jonsag/atTris/atTinyArcade-pio/src/Tetris_Attiny_Arcade.h

/* 2015 / 2016 /2017
   Tetris for Attiny Arcade
   ========================

   When the game is running :
   ==========================
   Tap LEFT BUTTON - Moves the piece to the left (and wraps around at the left edge)
   Hold LEFT BUTTON - Move the piece to the right
   Tap RIGHT BUTTON - Rotates the piece
   Hold RIGHT BUTTON - Place the piece

   Before the game starts:
   =======================
   Hold LEFT BUTTON - Turns 'ghost' piece on and off
   Hold RIGHT and LEFT BUTTONS together - Turns 'challenge mode' on and off (which fills the screens with random stuff at the start of the game to make
   it more tricky!)

   _________________________________________________________________________________________________________________________________________________________
   This version developed by Andy Jackson - Twitter @andyhighnumber - Tweet me if you have any problems getting this to compile or run.
   The code that does not fall under the licenses of sources listed below can be used non-commercially with or without attribution.
   This software is supplied without warranty of any kind.

   Designed for the Attiny85 and optimized for the #AttinyArcade platform. The source code is less than 8KB and the sketch
   should run happily with less than 300 bytes of RAM. You can find out more about this platform from http://webboggles.com/, buy kits
   to make it (or get instructions / schematics). This sketch includes some code from the #AttinyArcade games on that site, including interrupt code.

   This game started life as a port but is now essentially a clone of TinyTetris by Anthony Russell, with some additional features. There remain
   elements of that original codebase, although the vast majority of what's here has been rewritten from scratch (including the screen, text and number
   rendering code and much of the game engine) in order to optimize for memory, improve responsiveness and allow new features on the limited hardware
   (added features include High score (saved to EEPROM), optional Ghost (or Shadow) Piece, Interrupt Handling and Hard-Mode functionality).

   Anthony's source can be found here: https://github.com/AJRussell/Tiny-Tetris and is highly recommended if you'd like a version
   of Tetris to run on normal Arduino hardware. It has some lovely graphics by Tobozo (which sadly there's not space for on the Attiny85) and it's also
   possible that some code by Tobozo has made it into this version. Tobozo's repository can be found here; https://github.com/tobozo and is well worth a look.
   There is an Instructables page relating to this project here: https://www.instructables.com/id/Tetris-Clone-With-OLED-SSD1306I2C-for-Arduino-Nano/

   This sketch is using the screen control and font functions written by Neven Boyanov for the http://tinusaur.wordpress.com/ project
   Source code and font files available at: https://bitbucket.org/tinusaur/ssd1306xled - hacked about by Andy Jackson to make them
   render side-on for this game. All the necessary functions are in this file, there's no need to download any additional libraries to compile this game.

   The sleep code in this file is based on this blog post by Matthew Little:
   http://www.re-innovation.co.uk/web12/index.php/en/blog-75/306-sleep-modes-on-attiny85
*/

// The custom font file is the only additional file you should need to compile this game
#include "font8x8AJ.h"

// Standard Arduino headers
#include <EEPROM.h>
#include <avr/pgmspace.h>
#include <avr/sleep.h>
#include <avr/interrupt.h> // needed for the additional interrupt

// Mode settings for functions with multiple purposes
#define NORMAL 0
#define GHOST 1
#define FULL 0
#define PARTIAL 1
#define DRAW 0
#define ERASE 1

// The horizontal width of the playing area
#define HORIZ 10
// The vertical visible space of the playing area
#define VERTDRAW 19
// The size of the array of blocks (some are outside visible area to allow them to drop in from off screen)
#define VERTMAX 24

// The horizontal position where pieces begin
#define STARTX 3
// The vertical position where pieces begin
#define STARTY 19
// What level does the game start on
#define STARTLEVEL 1
// The multiplying factor that sets how the speed scales with level (one level increment for every row cleared)
#define LEVELFACTOR 4
// The number of milliseconds before each drop (baseline)
#define DROPDELAY 600

#define DIGITAL_WRITE_HIGH(PORT) PORTB |= (1 << PORT)
#define DIGITAL_WRITE_LOW(PORT) PORTB &= ~(1 << PORT)

// Routines to set and clear bits (used in the sleep code)
#define cbi(sfr, bit) (_SFR_BYTE(sfr) &= ~_BV(bit))
#define sbi(sfr, bit) (_SFR_BYTE(sfr) |= _BV(bit))

// Defines for OLED output
#define SSD1306XLED_H
#define SSD1306_SCL PORTB4 // SCL, Pin 4 on SSD1306 Board - for webbogles board
#define SSD1306_SDA PORTB3 // SDA, Pin 3 on SSD1306 Board - for webbogles board
#define SSD1306_SA 0x78    // Slave address

// The bitmaps for the little images of next block
static const byte miniBlock[][4] PROGMEM = {
    {0x77, 0x77, 0x00, 0x00},
    {0x70, 0x77, 0x70, 0x00},
    {0x70, 0x00, 0x70, 0x77},
    {0x70, 0x07, 0x70, 0x07},
    {0x70, 0x07, 0x00, 0xEE},
    {0x70, 0x77, 0x00, 0x0E},
    {0x70, 0x07, 0xEE, 0x00}};

// The bitmaps for the main blocks
static const int blocks[7] PROGMEM = {
    0x4444, 0x44C0,
    0x4460, 0x0660,
    0x06C0, 0x0E40,
    0x0C60};

// The bitmaps for blocks on the screen
static const byte blockout[16] PROGMEM = {
    0xF8, 0x00, 0x3E, 0x80,
    0x0F, 0xE0, 0x03, 0xF8,
    0x3E, 0x80, 0x0F, 0xE0,
    0x03, 0xF8, 0x3E, 0x00};

// The bitmaps for ghost blocks on the screen
static const byte ghostout[16] PROGMEM = {
    0x88, 0x00, 0x22, 0x80,
    0x08, 0x20, 0x02, 0x88,
    0x22, 0x80, 0x08, 0x20,
    0x02, 0x88, 0x22, 0x00};

// Decode lookup to translate block positions to the 8 columns on the screen
static const byte startDecode[11] PROGMEM = {0, 1, 1, 2, 3, 4, 4, 5, 6, 7, 8};
static const byte endDecode[11] PROGMEM = {1, 2, 3, 3, 4, 5, 6, 6, 7, 8, 8};

// Function prototypes - generic ones I use in all games
void doNumber(int x, int y, int value);
void beep(int, int);

// Function prototypes - screen control modified from https://bitbucket.org/tinusaur/ssd1306xled
void ssd1306_init(void);
void ssd1306_xfer_start(void);
void ssd1306_xfer_stop(void);
void ssd1306_send_byte(uint8_t byte);
void ssd1306_send_command(uint8_t command);
void ssd1306_send_data_start(void);
void ssd1306_send_data_stop(void);
void ssd1306_setpos(uint8_t x, uint8_t y);
void ssd1306_fillscreen(uint8_t fill_Data);
void ssd1306_char_f8x8(uint8_t x, uint8_t y, const char ch[]);

// Function prototypes - tetris-specific
void playTetris(void);
void handleInput(void);

void drawScreen(int startCol, int endCol, int startRow, int endRow, byte mode);
void drawScreenBorder(void);

byte readBlockArray(byte x, byte y);
void writeblockArray(byte x, byte y, bool value);
byte readGhostArray(byte x, byte y);
void writeGhostArray(byte x, byte y, bool value);
void fillGrid(byte value, bool mode);

void rotatePiece(void);
bool movePieceDown(void);
void movePieceLeft(void);
void movePieceRight(void);
byte checkCollision(void);

bool createGhost(void);
void drawGhost(byte action);
void loadPiece(byte pieceNumber, byte row, byte column);
void drawPiece(byte action);
void setNextBlock(byte pieceNumber);

// Variables
struct pieceSpace
{
  byte blocks[4][4];
  int row;
  int column;
};

pieceSpace currentPiece = {0}; // The piece in play
pieceSpace oldPiece = {0};     // Buffer to hold the current piece whilst its manipulated
pieceSpace ghostPiece = {0};   // Current ghost piece

unsigned long moveTime = 0; // Baseline time for current move
unsigned long keyTime = 0;  // Baseline time for current keypress

byte keylock = 0; // Holds the mode of the last keypress (for debounce and stuff)

byte nextBlockBuffer[8][2]; // The little image of the next block
byte nextPiece = 0;         // The identity of the next piece
byte blockArray[HORIZ][3];  // The byte-array of blocks
byte ghostArray[HORIZ][3];  // The byte-array of ghost pieces
bool stopAnimate;           // True when the game is running

int lastGhostRow = 0; // Buffer to hold previous ghost position - for accurate drawing
int score = 0;        // Score buffer
int topScore = 0;     // High score buffer

bool challengeMode = 0; // Is the system in "Hard" mode?
bool ghost = 1;         // Is the ghost active?

int level = 0; // Current level (increments once per cleared line)

void doNumber(int x, int y, int value)
{
  char temp[10] = {0, 0, 0, 0, 0, 0, 0, 0, 0, 0};
  itoa(value, temp, 10);
  ssd1306_char_f8x8(x, y, temp);
}

void beep(int bCount, int bDelay)
{
  for (int i = 0; i <= bCount; i++)
  {
    digitalWrite(1, HIGH);
    for (int i2 = 0; i2 < bDelay; i2++)
    {
      __asm__("nop\n\t");
    }
    digitalWrite(1, LOW);
    for (int i2 = 0; i2 < bDelay; i2++)
    {
      __asm__("nop\n\t");
    }
  }
}

void ssd1306_char_f8x8(uint8_t x, uint8_t y, const char ch[])
{
  uint8_t c, i, j = 0;

  while (ch[j] != '\0')
  {
    c = ch[j] - 32; // to space
    if (c > 0)
      c = c - 12; // to dash
    if (c > 15)
      c = c - 7;
    if (c > 40)
      c = c - 6;

    ssd1306_setpos(y, x);
    ssd1306_send_data_start();
    for (byte lxn = 0; lxn < 8; lxn++)
    {
      ssd1306_send_byte(pgm_read_byte(&font[c][7 - lxn]));
    }
    ssd1306_send_data_stop();
    x += 1;
    j++;
  }
}

// Interrupt handlers - to make sure every button press is caught promptly!
ISR(PCINT0_vect)
{ // PB0 pin button interrupt
  if (keylock == 0)
  {
    keylock = 1;
    keyTime = millis();
  }
}
void playerIncTetris()
{ // PB2 pin button interrupt
  if (keylock == 0)
  {
    keylock = 2;
    keyTime = millis();
  }
}

// Screen control functions
void ssd1306_init(void)
{
  DDRB |= (1 << SSD1306_SDA); // Set port as output
  DDRB |= (1 << SSD1306_SCL); // Set port as output

  ssd1306_send_command(0xAE); // display off
  ssd1306_send_command(0x00); // Set Memory Addressing Mode
  ssd1306_send_command(0x10); // 00,Horizontal Addressing Mode;01,VERTDRAWical Addressing Mode;10,Page Addressing Mode (RESET);11,Invalid
  ssd1306_send_command(0x40); // Set Page Start Address for Page Addressing Mode,0-7
  ssd1306_send_command(0x81); // Set COM Output Scan Direction
  ssd1306_send_command(0xCF); // ---set low column address
  ssd1306_send_command(0xA1); // ---set high column address
  ssd1306_send_command(0xC8); // --set start line address
  ssd1306_send_command(0xA6); // --set contrast control register
  ssd1306_send_command(0xA8);
  ssd1306_send_command(0x3F); // --set segment re-map 0 to 127
  ssd1306_send_command(0xD3); // --set normal display
  ssd1306_send_command(0x00); // --set multiplex ratio(1 to 64)
  ssd1306_send_command(0xD5); //
  ssd1306_send_command(0x80); // 0xa4,Output follows RAM content;0xa5,Output ignores RAM content
  ssd1306_send_command(0xD9); // -set display offset
  ssd1306_send_command(0xF1); // -not offset
  ssd1306_send_command(0xDA); // --set display clock divide ratio/oscillator frequency
  ssd1306_send_command(0x12); // --set divide ratio
  ssd1306_send_command(0xDB); // --set pre-charge period
  ssd1306_send_command(0x40); //
  ssd1306_send_command(0x20); // --set com pins hardware configuration
  ssd1306_send_command(0x02);
  ssd1306_send_command(0x8D); // --set vcomh
  ssd1306_send_command(0x14); // 0x20,0.77xVcc
  ssd1306_send_command(0xA4); // --set DC-DC enable
  ssd1306_send_command(0xA6); //
  ssd1306_send_command(0xAF); // --turn on oled panel
}

void ssd1306_xfer_start(void)
{
  DIGITAL_WRITE_HIGH(SSD1306_SCL); // Set to HIGH
  DIGITAL_WRITE_HIGH(SSD1306_SDA); // Set to HIGH
  DIGITAL_WRITE_LOW(SSD1306_SDA);  // Set to LOW
  DIGITAL_WRITE_LOW(SSD1306_SCL);  // Set to LOW
}

void ssd1306_xfer_stop(void)
{
  DIGITAL_WRITE_LOW(SSD1306_SCL);  // Set to LOW
  DIGITAL_WRITE_LOW(SSD1306_SDA);  // Set to LOW
  DIGITAL_WRITE_HIGH(SSD1306_SCL); // Set to HIGH
  DIGITAL_WRITE_HIGH(SSD1306_SDA); // Set to HIGH
}

void ssd1306_send_byte(uint8_t byte)
{
  uint8_t i;
  for (i = 0; i < 8; i++)
  {
    if ((byte << i) & 0x80)
      DIGITAL_WRITE_HIGH(SSD1306_SDA);
    else
      DIGITAL_WRITE_LOW(SSD1306_SDA);

    DIGITAL_WRITE_HIGH(SSD1306_SCL);
    DIGITAL_WRITE_LOW(SSD1306_SCL);
  }
  DIGITAL_WRITE_HIGH(SSD1306_SDA);
  DIGITAL_WRITE_HIGH(SSD1306_SCL);
  DIGITAL_WRITE_LOW(SSD1306_SCL);
}

void ssd1306_send_command(uint8_t command)
{
  ssd1306_xfer_start();
  ssd1306_send_byte(SSD1306_SA); // Slave address, SA0=0
  ssd1306_send_byte(0x00);       // write command
  ssd1306_send_byte(command);
  ssd1306_xfer_stop();
}

void ssd1306_send_data_start(void)
{
  ssd1306_xfer_start();
  ssd1306_send_byte(SSD1306_SA);
  ssd1306_send_byte(0x40); // write data
}

void ssd1306_send_data_stop(void)
{
  ssd1306_xfer_stop();
}

void ssd1306_setpos(uint8_t x, uint8_t y)
{
  if (y > 7)
    return;
  ssd1306_xfer_start();
  ssd1306_send_byte(SSD1306_SA); // Slave address,SA0=0
  ssd1306_send_byte(0x00);       // write command

  ssd1306_send_byte(0xb0 + y);
  ssd1306_send_byte(((x & 0xf0) >> 4) | 0x10); // |0x10
  ssd1306_send_byte((x & 0x0f) | 0x01);        // |0x01

  ssd1306_xfer_stop();
}

void ssd1306_fillscreen(uint8_t fill_Data)
{
  uint8_t m, n;
  for (m = 0; m < 8; m++)
  {
    ssd1306_send_command(0xb0 + m); // page0-page1
    ssd1306_send_command(0x00);     // low column start address
    ssd1306_send_command(0x10);     // high column start address
    ssd1306_send_data_start();
    for (n = 0; n < 128; n++)
    {
      ssd1306_send_byte(fill_Data);
    }
    ssd1306_send_data_stop();
  }
}

// Sleep code from http://www.re-innovation.co.uk/web12/index.php/en/blog-75/306-sleep-modes-on-attiny85
void system_sleep()
{
  ssd1306_fillscreen(0x00);
  ssd1306_send_command(0xAE);
  cbi(ADCSRA, ADEN);                   // switch Analog to DigitalconVERTDRAWer OFF
  set_sleep_mode(SLEEP_MODE_PWR_DOWN); // sleep mode is set here
  sleep_enable();
  sleep_mode();      // System actually sleeps here
  sleep_disable();   // System continues execution here when watchdog timed out
  sbi(ADCSRA, ADEN); // switch Analog to DigitalconVERTDRAWer ON
  ssd1306_send_command(0xAF);
}

byte readBlockArray(byte x, byte y)
{
  if (y < 8)
  {
    return ((blockArray[x][0] & B00000001 << y) >> y);
  }
  else if (y > 15)
  {
    return ((blockArray[x][2] & B00000001 << y - 15) >> y - 15);
  }
  else
  {
    return ((blockArray[x][1] & B00000001 << y - 8) >> y - 8);
  }
}

void writeblockArray(byte x, byte y, bool value)
{
  byte arr = 0;
  if (y < 8)
  {
    // do nothing
  }
  else if (y > 15)
  {
    arr = 2;
    y -= 15;
  }
  else
  {
    arr = 1;
    y -= 8;
  }
  if (value == 1)
    blockArray[x][arr] |= B00000001 << y;
  else
    blockArray[x][arr] &= (B11111110 << y) | (B01111111 >> 7 - y);
}

byte readGhostArray(byte x, byte y)
{
  if (y < 8)
  {
    return ((ghostArray[x][0] & B00000001 << y) >> y);
  }
  else if (y > 15)
  {
    return ((ghostArray[x][2] & B00000001 << y - 15) >> y - 15);
  }
  else
  {
    return ((ghostArray[x][1] & B00000001 << y - 8) >> y - 8);
  }
}

void writeGhostArray(byte x, byte y, bool value)
{
  byte arr = 0;
  if (y < 8)
  {
    // do nothing
  }
  else if (y > 15)
  {
    arr = 2;
    y -= 15;
  }
  else
  {
    arr = 1;
    y -= 8;
  }
  if (value == 1)
    ghostArray[x][arr] |= B00000001 << y;
  else
    ghostArray[x][arr] &= (B11111110 << y) | (B01111111 >> 7 - y);
}

void fillGrid(byte value, bool mode)
{
  for (char r = 0; r < VERTMAX; r++)
  {
    for (char c = 0; c < HORIZ; c++)
    {
      if (mode == GHOST)
        writeGhostArray(c, r, value);
      else
        writeblockArray(c, r, value);
    }
  }
}

void rotatePiece(void)
{
  byte blocks[4][4];

  memcpy(oldPiece.blocks, currentPiece.blocks, 16);
  oldPiece.row = currentPiece.row;
  oldPiece.column = currentPiece.column;

  for (byte i = 0; i < 4; ++i)
  {
    for (byte j = 0; j < 4; ++j)
    {
      blocks[j][i] = currentPiece.blocks[4 - i - 1][j];
    }
  }
  oldPiece = currentPiece;
  memcpy(currentPiece.blocks, blocks, 16);
  if (checkCollision())
    currentPiece = oldPiece;
  else
  {
    drawGhost(ERASE);
    if (createGhost())
      drawGhost(DRAW);
  }
}

void drawGameScreen(int startCol, int endCol, int startRow, int endRow, byte mode)
{
  drawScreen(startCol, endCol, startRow, endRow, mode);

  if (mode == PARTIAL)
  {
    if (ghostPiece.row < lastGhostRow)
    { // ghost has moved down :)
      drawScreen(startCol, endCol, ghostPiece.row, lastGhostRow + 4, mode);
    }
    else
    { // ghost has moved up (presumably!)
      drawScreen(startCol, endCol, lastGhostRow, ghostPiece.row + 4, mode);
    }
  }
}

bool movePieceDown(void)
{
  int rndPiece = 0;

  memcpy(oldPiece.blocks, currentPiece.blocks, 16);
  oldPiece.row = currentPiece.row;
  oldPiece.column = currentPiece.column;

  currentPiece.row--;

  // check collision
  if (checkCollision())
  {
    currentPiece.row = oldPiece.row;
    drawPiece(DRAW);
    byte totalRows = 0;

    for (byte row = 0; row < VERTMAX; row++)
    { // scan the whole block (it's quick - there's no drawing to do)
      bool rowFull = 1;
      for (byte col = 0; col < HORIZ; col++)
      { // scan across this row - every column
        if (readBlockArray(col, row) == 0)
          rowFull = 0; // if we hit any blank spaces, the row's not full
      }
      if (rowFull)
      {
        totalRows++;
        for (int i = 800; i > 200; i = i - 200)
          beep(30, i); // happy sound
        for (byte col = 0; col < HORIZ; col++)
          writeblockArray(col, row, 0);                      // write zeros across this whole row
        drawGameScreen(0, HORIZ - 1, row, row + 1, PARTIAL); // draw the row we're removing (for animation)
        delay(30);                                           // delay slightly to make the deletion of rows visible
        for (byte dropCol = 0; dropCol < HORIZ; dropCol++)
        { // for every column
          for (byte dropRow = row; dropRow < VERTMAX - 1; dropRow++)
            writeblockArray(dropCol, dropRow, readBlockArray(dropCol, dropRow + 1)); // drop everything down as many as the row's we've cleared
        }
        row--; // we need to check this row again as it could now have things in it!
      }
    }
    level += totalRows;
    switch (totalRows)
    {
    case 1:
      score += 40;
      break;
    case 2:
      score += 100;
      break;
    case 3:
      score += 300;
      break;
    case 4:
      score += 800;
    }
    drawGameScreen(0, 10, 0, VERTDRAW, FULL);
    loadPiece(nextPiece, STARTY, STARTX);
    if (checkCollision())
    {
      stopAnimate = true;
    }
    else
    {
      loadPiece(nextPiece, STARTY, STARTX);
      drawGhost(ERASE);
      if (createGhost())
        drawGhost(DRAW);
    }
    nextPiece = random(1, 8);
    setNextBlock(nextPiece);
  }
  drawGhost(ERASE);
  if (createGhost())
    drawGhost(DRAW);
}

void movePieceLeft(void)
{
  byte response;

  oldPiece = currentPiece;
  currentPiece.column = currentPiece.column - 1;

  response = checkCollision();

  if (response == 1)
  {
    currentPiece = oldPiece; // back to where it was
  }
  else if (response == 2)
  {
    int wide = 0;
    for (byte i = 0; i < 4; i++)
    {
      if (currentPiece.blocks[3][i])
        wide = 1;
    }
    boolean narrow = true;
    for (byte i = 0; i < 4; i++)
    {
      if (currentPiece.blocks[2][i])
        narrow = false;
    }
    if (narrow)
      wide = -1;
    currentPiece.column = 7 - wide;
    response = checkCollision(); // Check again - does wrapping around cause a collision?
    if (response == 1)
    {
      currentPiece = oldPiece; // back to where it was
    }
    else
    {
      drawGhost(ERASE);
      if (createGhost())
        drawGhost(DRAW);
      drawGameScreen(0, 10, 0, VERTDRAW, FULL);
    }
  }
  else
  {
    drawGhost(ERASE);
    if (createGhost())
      drawGhost(DRAW);
  }
}

void movePieceRight(void)
{
  oldPiece = currentPiece;
  currentPiece.column = currentPiece.column + 1;
  // check collision
  if (checkCollision())
  {
    currentPiece = oldPiece; // back to where it was
  }
  else
  {
    drawGhost(ERASE);
    if (createGhost())
      drawGhost(DRAW);
  }
}

byte checkCollision(void)
{
  byte pieceRow = 0;
  byte pieceColumn = 0;

  for (int c = currentPiece.column; c < currentPiece.column + 4; c++)
  {
    for (int r = currentPiece.row; r < currentPiece.row + 4; r++)
    {
      if (currentPiece.blocks[pieceColumn][pieceRow])
      {
        if (c < 0)
          return 2;
        if (c > 9)
          return 1;
        if (r < 0)
          return 1;
        if (c >= 0 && r >= 0 && c < HORIZ && r < VERTMAX)
        {
          if (readBlockArray(c, r))
          {
            return 1; // is it on landed blocks?
          }
        }
      }
      pieceRow++;
    }
    pieceRow = 0;
    pieceColumn++;
  }
  return 0;
}

void handleInput(void)
{
  if (digitalRead(2) == HIGH && keylock == 2 && millis() - keyTime > 300)
  {
    while (digitalRead(2) == HIGH)
    {
      drawPiece(ERASE);
      movePieceDown();
      drawPiece(DRAW);
      drawGameScreen(currentPiece.column, currentPiece.column + 4, currentPiece.row, currentPiece.row + 5, PARTIAL);
      delay(10);
      if (stopAnimate)
        return;
    }
    keylock = 0;
  }

  if (digitalRead(0) == HIGH && (keylock == 1 || keylock == 3) && millis() - keyTime > 200)
  {
    drawPiece(ERASE);
    movePieceRight();
    drawPiece(DRAW);
    drawGameScreen(currentPiece.column - 1, currentPiece.column + 4, currentPiece.row, currentPiece.row + 4, PARTIAL);
    keyTime = millis() + 100;
    keylock = 3;
  }

  if (digitalRead(0) == LOW && digitalRead(2) == LOW)
  {
    if (keylock == 2 && millis() - keyTime < 300)
    {
      drawPiece(ERASE);
      rotatePiece();
      drawPiece(DRAW);
      drawGameScreen(currentPiece.column, currentPiece.column + 4, currentPiece.row, currentPiece.row + 4, PARTIAL);
    }
    else if (keylock == 1)
    {
      drawPiece(ERASE);
      movePieceLeft();
      drawPiece(DRAW);
      drawGameScreen(currentPiece.column, currentPiece.column + 5, currentPiece.row, currentPiece.row + 4, PARTIAL);
    }
    keylock = 0;
  }
  delay(30);
}

void setNextBlock(byte pieceNumber)
{
  memset(nextBlockBuffer, 0, sizeof nextBlockBuffer); // clear buffer
  pieceNumber--;
  if (pieceNumber == 0)
  {
    for (int k = 2; k < 6; k++)
    {
      nextBlockBuffer[k][0] = pgm_read_byte(&miniBlock[pieceNumber][0]);
      nextBlockBuffer[k][1] = pgm_read_byte(&miniBlock[pieceNumber][0]);
    }
  }
  else
  {
    for (int k = 0; k < 3; k++)
    {
      nextBlockBuffer[k][0] = pgm_read_byte(&miniBlock[pieceNumber][0]);
      nextBlockBuffer[k][1] = pgm_read_byte(&miniBlock[pieceNumber][1]);
    }
    for (int k = 4; k < 7; k++)
    {
      nextBlockBuffer[k][0] = pgm_read_byte(&miniBlock[pieceNumber][2]);
      nextBlockBuffer[k][1] = pgm_read_byte(&miniBlock[pieceNumber][3]);
    }
  }
  drawGameScreen(0, 10, 0, VERTDRAW, FULL);
}

void drawScreenBorder(void)
{
  ssd1306_setpos(0, 0);
  ssd1306_send_data_start();
  ssd1306_send_byte(0xFF);
  for (byte c = 1; c < 126; c++)
  {
    ssd1306_send_byte(B00000001);
  }
  ssd1306_send_byte(0xFF);
  ssd1306_send_data_stop();

  for (byte r = 1; r < 7; r++)
  {
    ssd1306_setpos(0, r);
    ssd1306_send_data_start();
    ssd1306_send_byte(0xFF);
    for (byte c = 1; c < 126; c++)
    {
      ssd1306_send_byte(B00000000);
    }
    ssd1306_send_byte(0xFF);
  }
  ssd1306_send_data_stop();

  ssd1306_setpos(0, 7);
  ssd1306_send_data_start();
  ssd1306_send_byte(0xFF);
  for (byte c = 1; c < 126; c++)
  {
    ssd1306_send_byte(B10000000);
  }
  ssd1306_send_byte(0xFF);
  ssd1306_send_data_stop();
}

void displayScore(int score, int xpos, int y, bool blank)
{
  byte scoreOut[6];
  scoreOut[5] = (score % 10);
  scoreOut[4] = ((score / 10) % 10);
  scoreOut[3] = ((score / 100) % 10);
  scoreOut[2] = ((score / 1000) % 10);
  scoreOut[1] = ((score / 10000) % 10);
  scoreOut[0] = ((score / 100000) % 10);

  for (byte x = xpos; x < xpos + 6; x++)
  {
    ssd1306_setpos(y, x);
    ssd1306_send_data_start();
    for (byte lxn = 0; lxn < 8; lxn++)
    {
      if (blank)
        ssd1306_send_byte(0);
      else
        ssd1306_send_byte(pgm_read_byte(&font[4 + scoreOut[x - xpos]][7 - lxn]));
    }
    ssd1306_send_data_stop();
  }
}

void drawScreen(int startCol, int endCol, int startRow, int endRow, byte mode)
{
  byte temp = 0;
  byte separator = 0;
  byte scoreOut[6];
  byte reader = 0;
  byte blockReader = 0;

  if (startCol < 0)
    startCol = 0;
  if (endCol > 10)
    endCol = 10;
  if (startRow < 0)
    startRow = 0;
  if (endRow > VERTDRAW)
    endRow = VERTDRAW;

  byte startScreenCol = pgm_read_byte(&startDecode[startCol]);
  byte endScreenCol = pgm_read_byte(&endDecode[endCol]);

  scoreOut[5] = (score % 10);
  scoreOut[4] = ((score / 10) % 10);
  scoreOut[3] = ((score / 100) % 10);
  scoreOut[2] = ((score / 1000) % 10);
  scoreOut[1] = ((score / 10000) % 10);
  scoreOut[0] = ((score / 100000) % 10);

  for (byte col = startScreenCol; col < endScreenCol; col++)
  {
    if (col < 4)
      reader = col;
    else if (col < 7)
      reader = col + 1;
    else
      reader = col + 2;
    blockReader = 2 * col;
    ssd1306_setpos(startRow * 6, col); // Start from the end of this column (working up the screen) on the required row
    ssd1306_send_data_start();
    if (startRow == 0)
      ssd1306_send_byte(B11111111);
    else
    {
      if (col == 0)
        ssd1306_send_byte(B00000001);
      else if (col == 7)
        ssd1306_send_byte(B10000000);
      else
        ssd1306_send_byte(B00000000);
    }
    for (byte r = startRow; r < endRow; r++)
    { // For each row in the array of tetris blocks
      for (byte piece = 0; piece < 5; piece++)
      { // for each of the 5 filled lines of the block
        if (col == 0)
          temp = B00000001;
        else if (col == 7)
          temp = B10000000;
        else
          temp = 0x00;    // if we're on the far left, draw the left wall, on the far right draw the right wall, otherwise its a blank separator between blocks
        separator = temp; // we'll need this again later!

        if (readBlockArray(reader, r))
        {
          temp = temp | pgm_read_byte(&blockout[blockReader]);
        }
        if (readBlockArray(reader + 1, r))
        {
          temp = temp | pgm_read_byte(&blockout[blockReader + 1]);
        }

        if (ghost)
        {
          if (readGhostArray(reader, r) && (piece == 0 || piece == 4))
          {
            temp = temp | pgm_read_byte(&blockout[blockReader]);
          }
          else if (readGhostArray(reader, r))
          {
            temp = temp | pgm_read_byte(&ghostout[blockReader]);
          }

          if (readGhostArray(reader + 1, r) && (piece == 0 || piece == 4))
          {
            temp = temp | pgm_read_byte(&blockout[blockReader + 1]);
          }
          else if (readGhostArray(reader + 1, r))
          {
            temp = temp | pgm_read_byte(&ghostout[blockReader + 1]);
          }
        }
        ssd1306_send_byte(temp);
      }
      ssd1306_send_byte(separator); // between blocks - same one as we used at the start
    }
    if (mode == FULL)
      if (col < 6)
        for (byte numline = 0; numline < 8; numline++)
          ssd1306_send_byte(pgm_read_byte(&font[scoreOut[col] + 4][7 - numline]));
      else
        for (byte blockline = 0; blockline < 8; blockline++)
          ssd1306_send_byte(nextBlockBuffer[blockline][col - 6]);
    ssd1306_send_data_stop();
  }
}

bool createGhost(void)
{
  byte tempRow = currentPiece.row;

  if (currentPiece.row < 3)
    return 0;

  currentPiece.row -= 2;
  while (checkCollision() == 0)
    currentPiece.row--;

  memcpy(ghostPiece.blocks, currentPiece.blocks, 16);
  ghostPiece.row = currentPiece.row + 1;
  ghostPiece.column = currentPiece.column;
  currentPiece.row = tempRow;

  if (ghostPiece.row > currentPiece.row - 3)
    return 0;
  else
    return 1;
}

void loadPiece(byte pieceNumber, byte row, byte column)
{
  byte incr = 0;

  pieceNumber--;

  for (byte lxn = 0; lxn < 4; lxn++)
  {
    for (byte lxn2 = 0; lxn2 < 4; lxn2++)
    {
      if (((1 << incr) & pgm_read_word(&blocks[pieceNumber])) >> incr == 1)
      {
        currentPiece.blocks[lxn][lxn2] = 1;
      }
      else
        currentPiece.blocks[lxn][lxn2] = 0;
      incr++;
    }
  }
  currentPiece.row = row;
  currentPiece.column = column;
}

void drawPiece(byte action)
{
  for (byte lxn = 0; lxn < 4; lxn++)
  {
    for (byte lxn2 = 0; lxn2 < 4; lxn2++)
    {
      if (currentPiece.blocks[lxn][lxn2] == 1)
      {
        if (action == DRAW)
          writeblockArray(currentPiece.column + lxn, currentPiece.row + lxn2, 1);
        else if (action == ERASE)
          writeblockArray(currentPiece.column + lxn, currentPiece.row + lxn2, 0);
      }
    }
  }
}

void drawGhost(byte action)
{
  for (byte lxn = 0; lxn < 4; lxn++)
  {
    for (byte lxn2 = 0; lxn2 < 4; lxn2++)
    {
      if (ghostPiece.blocks[lxn][lxn2] == 1)
      {
        if (action == DRAW)
          writeGhostArray(ghostPiece.column + lxn, ghostPiece.row + lxn2, 1);
        else if (action == ERASE)
        {
          writeGhostArray(ghostPiece.column + lxn, ghostPiece.row + lxn2, 0);
          lastGhostRow = ghostPiece.row;
        }
      }
    }
  }
}

void playTetris(void)
{
  stopAnimate = 0;
  score = 0;

  fillGrid(0, NORMAL);
  fillGrid(0, GHOST);

  // Attach the interrupt to read key 2
  attachInterrupt(0, playerIncTetris, RISING);

  loadPiece(random(1, 8), STARTY, STARTX);
  drawPiece(DRAW);
  if (createGhost())
    drawGhost(DRAW);
  drawGhost(DRAW);
  nextPiece = random(1, 8);
  setNextBlock(nextPiece);

  // Fill up the screen with random crap if it's in challenge mode!
  if (challengeMode)
  {
    for (byte cl = 0; cl < 100; cl++)
    {
      drawPiece(ERASE);
      movePieceDown();
      if (random(1, 8) > 4)
        movePieceLeft();
      drawPiece(DRAW);
    }
  }

  // Reset the level
  level = STARTLEVEL;

  drawGameScreen(0, 10, 0, VERTDRAW, FULL);

  while (stopAnimate == 0)
  {
    drawPiece(ERASE);
    movePieceDown();
    drawPiece(DRAW);
    drawGameScreen(currentPiece.column, currentPiece.column + 4, currentPiece.row, currentPiece.row + 5, PARTIAL);
    moveTime = millis();
    if (level * LEVELFACTOR > DROPDELAY)
      level = DROPDELAY / LEVELFACTOR;
    while ((millis() - moveTime) < (DROPDELAY - level * LEVELFACTOR))
    {
      handleInput();
    }
  }

  ssd1306_fillscreen(0x00);

  bool newHigh = false;
  topScore = EEPROM.read(0);
  topScore = topScore << 8;
  topScore = topScore | EEPROM.read(1);

  if (score > topScore)
  {
    topScore = score;
    EEPROM.write(1, score & 0xFF);
    EEPROM.write(0, (score >> 8) & 0xFF);
    newHigh = true;
  }
  drawScreenBorder();

  displayScore(score, 1, 80, 0);
  displayScore(topScore, 1, 40, 0);
  for (int i = 0; i < 1000; i = i + 50)
  {
    beep(50, i);
  }
  for (byte lx = 0; lx < 4; lx++)
  {
    displayScore(score, 1, 80, 1);
    if (newHigh)
      displayScore(topScore, 1, 40, 1);
    delay(200);
    displayScore(score, 1, 80, 0);
    if (newHigh)
      displayScore(topScore, 1, 40, 0);
    delay(200);
  }
}

// Arduino stuff
void setup()
{
  DDRB = 0b00000010;   // set PB1 as output (for the speaker)
  PCMSK = 0b00000001;  // pin change mask: listen to portb bit 1
  GIMSK |= 0b00100000; // enable PCINT interrupt
  sei();               // enable all interrupts
  ssd1306_init();      // initialise the screen
  keylock = 0;
}

void loop()
{
  ssd1306_init();
  ssd1306_fillscreen(0x00);

  ssd1306_char_f8x8(0, 88, " ------ ");
  ssd1306_char_f8x8(0, 80, " TETRIS ");
  ssd1306_char_f8x8(0, 72, " ------ ");
  ssd1306_char_f8x8(0, 64, " Attiny ");
  ssd1306_char_f8x8(0, 56, " Arcade ");
  ssd1306_char_f8x8(0, 48, " ------ ");

  long startT = millis();
  long nowT = 0;
  boolean sChange = 0;
  while (digitalRead(0) == HIGH)
  {
    nowT = millis();
    if (nowT - startT > 2000)
    {
      sChange = 1;
      if (digitalRead(2) == HIGH)
      {
        if (challengeMode == 0)
        {
          challengeMode = 1;
          ssd1306_char_f8x8(0, 16, "  HARD ");
          ssd1306_char_f8x8(0, 8, "  MODE ");
        }
        else
        {
          challengeMode = 0;
          ssd1306_char_f8x8(0, 16, " NORMAL");
          ssd1306_char_f8x8(0, 8, "  MODE ");
        }
      }
      else if (ghost == 0)
      {
        ghost = 1;
        ssd1306_char_f8x8(0, 16, " GHOST ");
        ssd1306_char_f8x8(0, 8, "  ON   ");
      }
      else
      {
        ghost = 0;
        ssd1306_char_f8x8(0, 16, " GHOST ");
        ssd1306_char_f8x8(0, 8, "  OFF  ");
      }
      break;
    }
    if (sChange == 1)
      break;
  }
  while (digitalRead(0) == HIGH)
    ;
  if (sChange == 0)
  {
    delay(2500);
    ssd1306_fillscreen(0x00);
    playTetris();
  }
  delay(1000);
  system_sleep();
}
